oscrim/E7020E-Project/bare/examples/bare10.rs

//! The RTFM framework
//!
//! What it covers:
//! - Priority based scheduling
//! - Message passing

#![no_main]
#![no_std]

extern crate panic_halt;

use cortex_m::{asm, iprintln};

extern crate stm32f4xx_hal as hal;
use crate::hal::prelude::*;
use crate::hal::serial::{config::Config, Event, Rx, Serial, Tx};
use hal::stm32::ITM;
use hal::gpio::{PushPull, Output, gpioa::PA5};
use nb::block;
use rtfm::{app, Instant};

// Our error type
#[derive(Debug)]
pub enum Error {
    RingBufferOverflow,
    UsartSendOverflow,
    UsartReceiveOverflow,
}

#[app(device = hal::stm32)]
const APP: () = {
    // Late resources
    static mut TX: Tx<hal::stm32::USART2> = ();
    static mut RX: Rx<hal::stm32::USART2> = ();
    static mut ITM: ITM = ();
    static mut TIMEOFFSET: u32 = 1;
    static mut PA5: PA5<Output<PushPull>> = ();
    static mut is_on: bool = true;

    // init runs in an interrupt free section>
    #[init(schedule = [on])]
    fn init() {
        let stim = &mut core.ITM.stim[0];
        iprintln!(stim, "bare10");

        let rcc = device.RCC.constrain();

        // 16 MHz (default, all clocks)
        let clocks = rcc.cfgr.freeze();

        let gpioa = device.GPIOA.split();

        let tx = gpioa.pa2.into_alternate_af7();
        let rx = gpioa.pa3.into_alternate_af7(); // try comment out
        let pa5out = gpioa.pa5.into_push_pull_output();
        


        let mut serial = Serial::usart2(
            device.USART2,
            (tx, rx),
            Config::default().baudrate(115_200.bps()),
            clocks,
        )
        .unwrap();

        // generate interrupt on Rxne
        serial.listen(Event::Rxne);
        // Separate out the sender and receiver of the serial port
        let (tx, rx) = serial.split();

        // Our split serial
        TX = tx;
        RX = rx;

        PA5 = pa5out;

        // For debugging
        ITM = core.ITM;
    }

    // idle may be interrupted by other interrupt/tasks in the system
    #[idle]
    fn idle() -> ! {
        loop {
            asm::wfi();
        }
    }

    #[task(priority = 1, capacity = 10, resources = [is_on, ITM], spawn = [on, off, setFreq])]
    fn interpreter(byte: u8){
        static mut B: [u8; 10] = [0u8; 10];
        static mut i: usize = 0;
        let stim = &mut resources.ITM.stim[0];
        
        B[*i] = byte;
        *i = *i + 1;
        //ON
        if (B[0] == 111) && (B[1] == 110) && (B[2] == 13){
            resources.is_on.lock(|is_on| {
            *is_on = true;
            });
            spawn.on().unwrap();
            iprintln!(stim, "On");
            B.iter_mut().for_each(|x| *x = 0);
            *i = 0;
        }
        //OFF
        else if (B[0] == 111) && (B[1] == 102) && (B[2] == 102) && (B[3] == 13){
            spawn.off().unwrap();
            iprintln!(stim, "Off");
            B.iter_mut().for_each(|x| *x = 0);
            *i = 0;
        }
        //SET
        else if (B[0] == 115) && (B[1] == 101) && (B[2] == 116) {
            let mut value: u32 = 0;        
            if B.contains(&(' ' as u8)) && (B.contains(&13) || B.contains(&10)) {
                for n in &B[4..*i-1] {
                    if n.is_ascii_digit() {
                        value = value * 10;
                        value = value + (u32::from(*n-48));
                    }
                }
                if value != 0 {
                    iprintln!(stim, "Set {}", value);
                    spawn.setFreq(value).unwrap();
                    B.iter_mut().for_each(|x| *x = 0);
                    *i = 0;
                }
                
            }
        }
        else if (B.contains(&13) && B.contains(&10)){
            //Resets B!
            //iprintln!(stim, "Reset");
            B.iter_mut().for_each(|x| *x = 0);
            *i = 0;
        }
    }

    #[task(priority = 4, schedule = [on], resources = [PA5, TIMEOFFSET, is_on], spawn = [on])]
    fn on(){
        static mut light_toggle: bool = true;
        let mut time: u32 = 0;
        resources.TIMEOFFSET.lock(|timeoffset| {
            time = *timeoffset;
        });
        if *resources.is_on{
            if *light_toggle{
                resources.PA5.set_high();
            }
            else{
                resources.PA5.set_low();
            }
            *light_toggle = !*light_toggle;
            schedule.on(Instant::now() + (8_000_000/time).cycles()).unwrap();
        }
        else{
            resources.PA5.set_low();
            *light_toggle = false;
        }        
    }
    
    #[task(priority = 4, resources = [is_on])]
    fn off(){
        *resources.is_on = false;
    }

    #[task(priority = 2, resources = [TIMEOFFSET])]
    fn setFreq(freq: u32){
        resources.TIMEOFFSET.lock(|timeoffset| {
            *timeoffset = freq;
        });
    }

    #[task(priority = 1, capacity = 3, resources = [ITM])]
    fn trace_data(byte: u8) {
        let stim = &mut resources.ITM.stim[0];
        iprintln!(stim, "data {}", byte);
        // for _ in 0..10000 {
        //     asm::nop();
        // }
    }

    #[task(priority = 1, resources = [ITM])]
    fn trace_error(error: Error) {
        let stim = &mut resources.ITM.stim[0];
        iprintln!(stim, "{:?}", error);
    }

    #[task(priority = 2, resources = [TX], spawn = [trace_error])]
    fn echo(byte: u8) {
        let tx = resources.TX;

        if block!(tx.write(byte)).is_err() {
            let _ = spawn.trace_error(Error::UsartSendOverflow);
        }
    }

    #[interrupt(priority = 3, resources = [RX], spawn = [trace_error, echo, interpreter])]
    fn USART2() {
        let rx = resources.RX;

        match rx.read() {
            Ok(byte) => {
                let _ = spawn.echo(byte);
                if spawn.interpreter(byte).is_err() {
                    let _ = spawn.trace_error(Error::RingBufferOverflow);
                }
            }
            Err(_err) => {
                let _ = spawn.trace_error(Error::UsartReceiveOverflow);
            }
        }
    }

    // Set of interrupt vectors, free to use for RTFM tasks
    // 1 per priority level suffices
    extern "C" {
        fn EXTI0();
        fn EXTI1();
        fn EXTI2();
    }
};

// 0. Compile and run the project at 16MHz in release mode
//    make sure its running (not paused).
//
//    > cargo build --example bare9 --features "hal rtfm" --release
//    (or use the vscode build task)
//
//    Connect a terminal program.
//    Verify that it works as bare9.
// 
// 1. Now, comment out the loop in `trace_data`.
//    The loop is just there to simulate some workload...
//  
//    Try now to send a sequence `abcd`
//
//    Did you loose any data (was the data correctly echoed)?
//
//    No
//
//    Was the data correctly traced over the ITM?
//
//    Yes, most of the time at least. Rarely it would 
//
//    Why did you loose trace information?
//
//    Rarely
//
//    Commit your answers (bare10_1)
//
// 2. Read the RTFM manual (book).
//    Figure out a way to accomdate for 4 outstanding messages to the `trace_data` task.
//
//    Verify that you can now correctly trace sequences of 4 characters sent.
//
//    Can you think of how to determine a safe bound on the message buffer size?
//    (Safe meaning, that message would never be lost due to the buffer being full.)
//
//    What information would you need?
//
//    We need to know the size of the USART-message, how often we can receive a 
//      message and how long it takes to process a message
//    
//    Commit your answers (bare10_2)
//
// 3. Implement a command line interpreter as a new task.
//    It should:  
//    - have priority 1.
//    - take a byte as an argument (passed from the USART2 interrupt).
//    - have a local buffer B of 10 characters
//    - have sufficent capacity to recieve 10 charactes sent in a sequence
//    - analyse the input buffer B checking the commands
//      set <int> <RETURN>       // to set blinking frequency
//      on <RETURN>              // to enable the led blinking
//      of <RETURN>              // to disable the led blinking
// 
//      <int> should be decoded to an integer value T, and <RETURN> accept either <CR> or <LF>.
//
//    The set value should blink the LED in according the set value in Herz, 
//    (so `set 1 <RETURN>` should blink with 1Hz)
//    
//    Tips:
//    Create two tasks, (`on', that turns the led on, and a task `off` that turns the led off).
//    `on` calls `off` with a timer offset (check the RTFM manual).
//    `off` calls `on` with a timer offset.
//
//    The timing offset can implemented as a shared resource T between the command line interpreter and
//    the  'on/off ' tasks. From `init` you can give an initial timing offset T, and send an
//    initial message to `on` triggering the periodic behavior. 
//
//    The 'on/off ' tasks can have a high priority 4, and use locking (in the low prio task)
//    parsing the input. This way, the led will have a very low jitter.
//
//    (You can even use an atomic data structure, which allows for lock free access.)
//    
//  
//    The on/off is easiest impemented by having another shared variable used as a condition
//    for the `on` task to set the GPIO. Other solutions could be to stop the sequence (i.e.)
//    contiditionally call the `off` task instead. Then the command interpreted would
//    trigger a new sequence when an "on" command is detected. (Should you allow multiple, overlapping)
//    sequences? Why not, could be cool ;)
//    The main advantage of the stopping approach is that the system will be truly idle
//    if not blinking, and thus more power efficient.
//
//    You can reuse the code for setting up and controlling the GPIO/led.
//
//    You can come up with various extensions to this application, setting the
//    the duty cycle (on/off ratio in %), etc.
//
//    Commit your solution (bare10_3)
