oscrim/E7020E-Project/bare/examples/itm.rs

//! Sends "Hello, agian!" over the ITM port 0
//!
//! ITM is much faster than semihosting. Like 4 orders of magnitude or so.
//!
//! You'll need [`itmdump`] to receive the message on the host plus you'll need to uncomment two
//! `monitor` commands in the `.gdbinit` file.
//!
//! [`itmdump`]: https://docs.rs/itm/0.2.1/itm/
//!
//! ---

#![no_main]
#![no_std]

extern crate panic_halt;

use cortex_m::{iprintln, Peripherals};
use cortex_m_rt::entry;

#[entry]
fn main() -> ! {
    let mut p = Peripherals::take().unwrap();
    let stim = &mut p.ITM.stim[0];

    iprintln!(stim, "Hello, again!");
    loop {}
}
